AVarfolomeev/tcs34725_par_meter2/Core/Src/spi1106.c

/*
 * spi1106.c
 * Library for SPI SH1106 OLED Display
 * v1.0 Created on: 10 aug 2020
 * Author: Maksim Ilyin imax9@narod.ru
 */

#include "main.h"
#include "spi1106.h"

extern SPI_HandleTypeDef hspi1;

const uint8_t SmallFont[] =
{												//
0x00, 0x00, 0x00, 0x00, 0x00, 0x00,
0x00, 0x00, 0x00, 0x2F, 0x00, 0x00,				//	002)	0x21=033	!
0x00, 0x00, 0x07, 0x00, 0x07, 0x00,				//	003)	0x22=034	"
0x00, 0x14, 0x7F, 0x14, 0x7F, 0x14,				//	004)	0x23=035	#
0x00, 0x24, 0x2A, 0x7F, 0x2A, 0x12,				//	005)	0x24=036	$
0x00, 0x23, 0x13, 0x08, 0x64, 0x62,				//	006)	0x25=037	%
0x00, 0x36, 0x49, 0x55, 0x22, 0x50,				//	007)	0x26=038	&
0x00, 0x00, 0x05, 0x03, 0x00, 0x00,				//	008)	0x27=039	'
0x00, 0x00, 0x1C, 0x22, 0x41, 0x00,				//	009)	0x28=040	(
0x00, 0x00, 0x41, 0x22, 0x1C, 0x00,				//	010)	0x29=041	)
0x00, 0x14, 0x08, 0x3E, 0x08, 0x14,				//	011)	0x2A=042	*
0x00, 0x08, 0x08, 0x3E, 0x08, 0x08,				//	012)	0x2B=043	+
0x00, 0x00, 0x00, 0xA0, 0x60, 0x00,				//	013)	0x2C=044	,
0x00, 0x08, 0x08, 0x08, 0x08, 0x08,				//	014)	0x2D=045	-
0x00, 0x00, 0x60, 0x60, 0x00, 0x00,				//	015)	0x2E=046	.
0x00, 0x20, 0x10, 0x08, 0x04, 0x02,				//	016)	0x2F=047	/
												//
0x00, 0x3E, 0x51, 0x49, 0x45, 0x3E,				//	017)	0x30=048	0
0x00, 0x00, 0x42, 0x7F, 0x40, 0x00,				//	018)	0x31=049	1
0x00, 0x42, 0x61, 0x51, 0x49, 0x46,				//	019)	0x32=050	2
0x00, 0x21, 0x41, 0x45, 0x4B, 0x31,				//	020)	0x33=051	3
0x00, 0x18, 0x14, 0x12, 0x7F, 0x10,				//	021)	0x34=052	4
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
}

HAL_StatusTypeDef SPI_Transmit(SPI_HandleTypeDef *hspi, uint8_t *pData, uint16_t Size)
{
	return HAL_SPI_Transmit(hspi, pData, Size, 1000);
}

void sh1106Clear(uint8_t start, uint8_t stop)
{
	uint32_t *adrclear;
	uint32_t timep,timec;
	uint8_t dt[128];

	adrclear = (uint32_t*)dt;
	for(uint8_t i=0;i<32;i++) {*adrclear++=0x00;}
	for (uint8_t m = start; m <= stop; m++)
	{
		SH1106_WC(0xB0+m);
		SH1106_WC(2);
		SH1106_WC(0x10);
		SH_Data;
		SH_CsLo;
		SPI_Transmit(&hspi1, dt, 128);
		timec=HAL_GetTick();
		timep=timec+50;
		while ((HAL_SPI_GetState(&hspi1) != HAL_SPI_STATE_READY)&&(timec<timep))
		{
			timec=HAL_GetTick();
		}
		SH_CsHi;
	}
}
void sh1106SmallPrint(uint8_t posx, uint8_t posy, uint8_t *str)
{
 uint8_t dt[128];
 uint16_t posfont, posscr;
 uint32_t *adrclear;
 uint32_t timer,timec;
 adrclear=&dt;
 uint8_t code;
 code=*str++;
 for(uint8_t i=0;i<32;i++) { *adrclear++=0; }
 posscr=posx*6;
 while (code>31)
 {
  if(code==32) {posscr+=2;}
  else
  {posfont=6*(code-32);
   for(uint8_t i = 0; i <6; i++)
    {dt[i+posscr]=SmallFont[i+posfont];}
  posscr+=6;
 }
 code=*str++;
 if (posscr>122) break;
}
  SH1106_WC(0xB0+posy);
  SH1106_WC(2);
  SH1106_WC(0x10);
  SH_Data;
  SH_CsLo;
  SPI_Transmit(&hspi1, dt, 128);
  timec=HAL_GetTick();
  timer=timec+50;
  while ((HAL_SPI_GetState(&hspi1) != HAL_SPI_STATE_READY)&&(timec<timer))
   {timec=HAL_GetTick();}
  SH_CsHi;
}
void sh1106MediumPrint(uint8_t posx, uint8_t posy, uint8_t *str)
{	uint8_t dt[256];
	uint16_t posfont, posscr;
	uint32_t *adrclear;
	uint32_t timer,timec;
	adrclear=&dt;
	uint8_t code;
	code=*str++;
	for(uint8_t i=0;i<64;i++) { *adrclear++=0; }
	posscr=posx*12;
while (code>31)
{posfont=24*(code-32);
 for(uint8_t i = 0; i <12; i++)
 {dt[i+posscr]=MediumFont[i+posfont];
  dt[i+128+posscr]=MediumFont[i+12+posfont];}
	code=*str++;
	posscr+=12;
	if (posscr>116) break;
 }
 SH1106_WC(0xB0+posy);
 SH1106_WC(2);
 SH1106_WC(0x10);
 SH_Data;
 SH_CsLo;
 SPI_Transmit(&hspi1, dt, 128);
 timec=HAL_GetTick();
 timer=timec+50;
 while ((HAL_SPI_GetState(&hspi1) != HAL_SPI_STATE_READY)&&(timec<timer))
 {timec=HAL_GetTick();}
 SH1106_WC(0xB0+posy+1);
 SH1106_WC(2);
 SH1106_WC(0x10);
 SH_Data;
 SH_CsLo;
 SPI_Transmit(&hspi1, dt + 128, 128);
 timec=HAL_GetTick();
 timer=timec+50;
 while ((HAL_SPI_GetState(&hspi1) != HAL_SPI_STATE_READY)&&(timec<timer))
 {timec=HAL_GetTick();}
 SH_CsHi;
}
